martinsram3k/Node-Smart-Clock/pcb/esp_smart_clock/esp_smart_clock.kicad_sch

## KiCad design pcb/esp_smart_clock/esp_smart_clock.kicad_sch (2026-01-16)

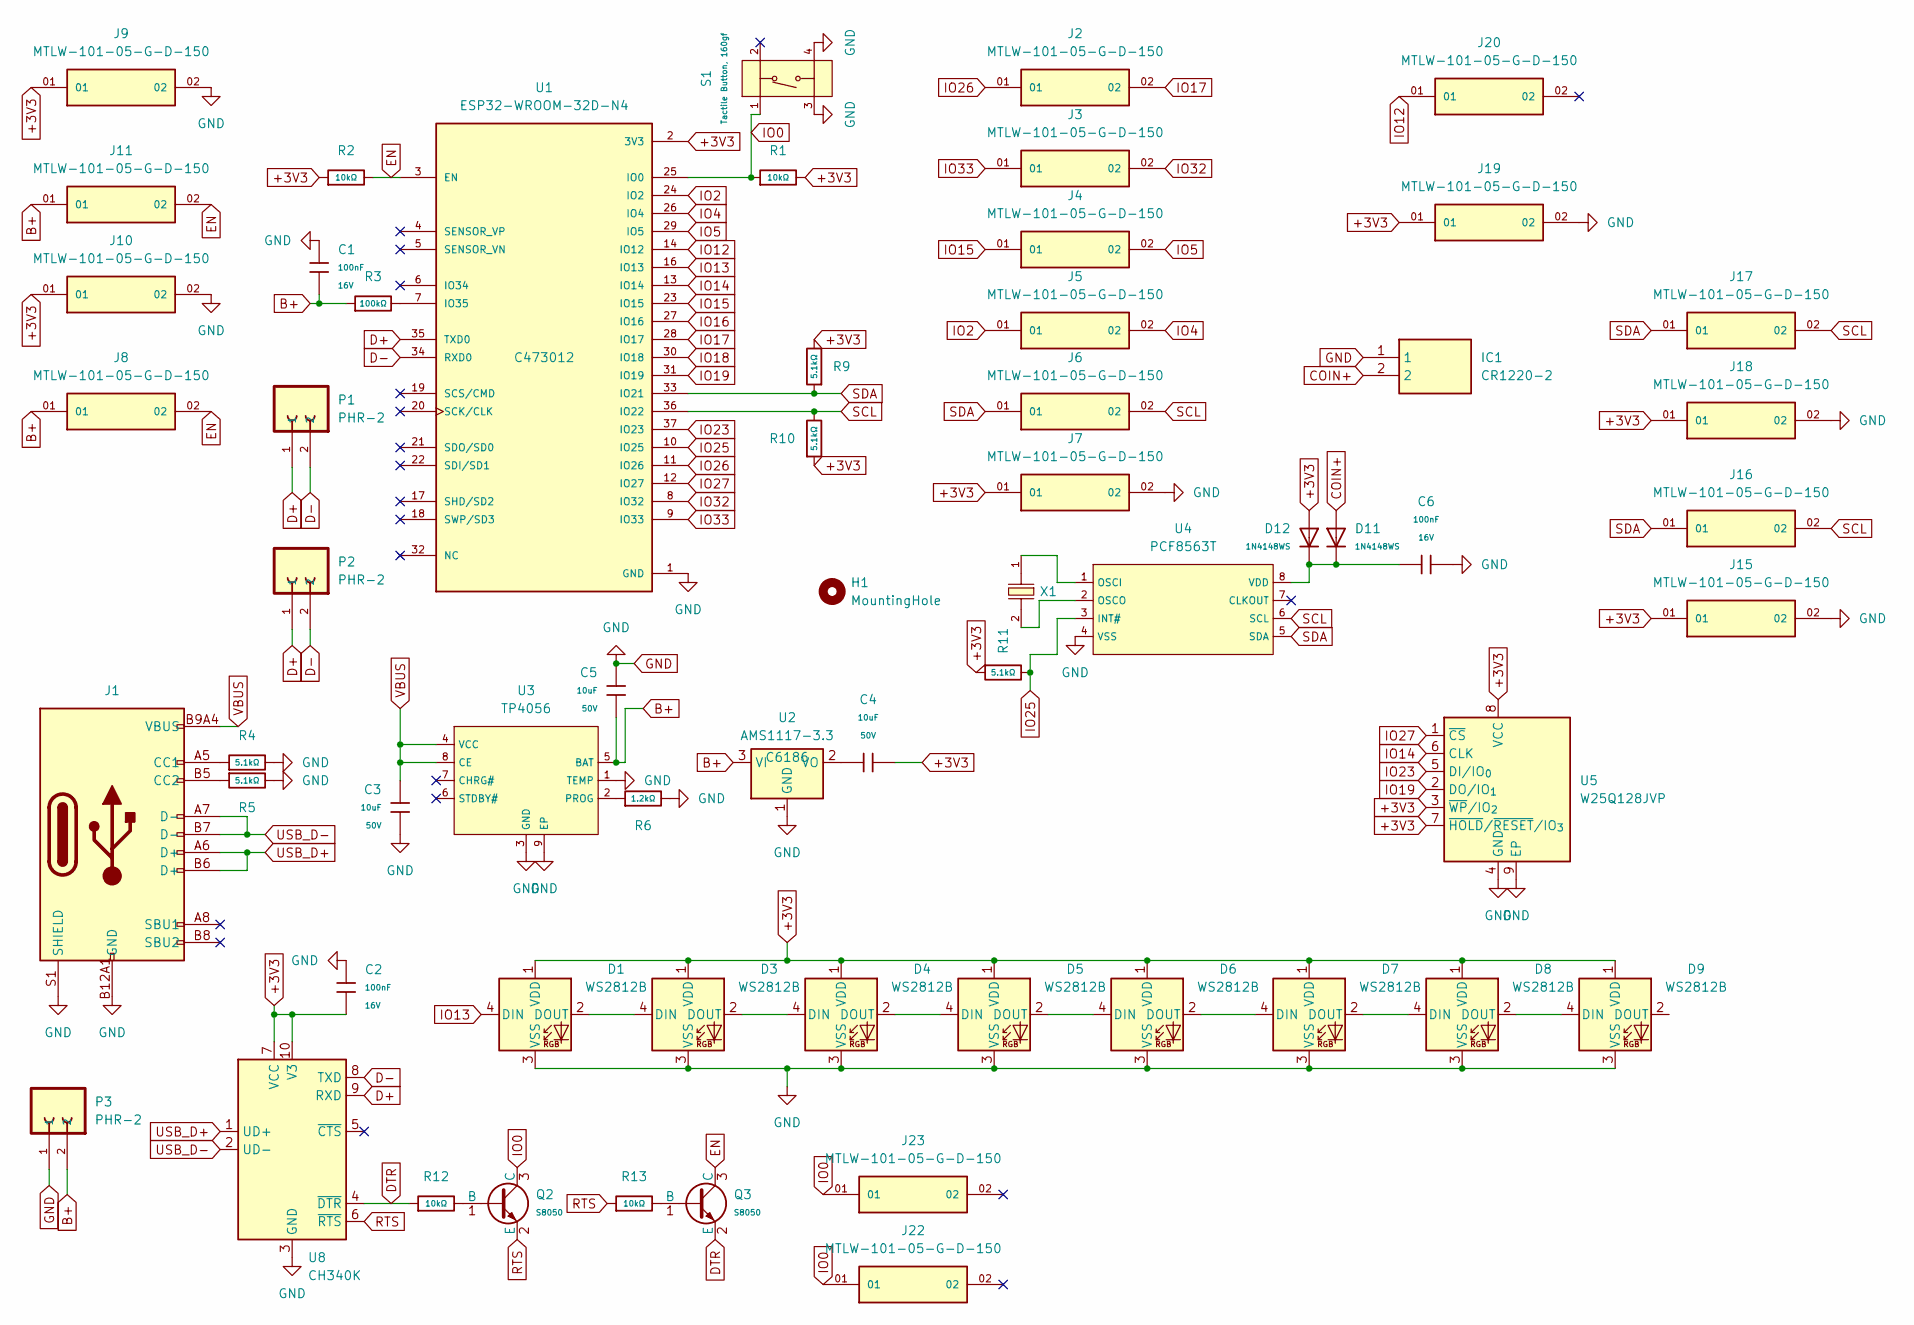
[picture p9: schematic esp_smart_clock.kicad_sch]

Parts:
C1, C2, C6: 100nF; C_0402; Voltage Rated 16V; Tolerance ±10%; Part CL05B104KO5NNNC; LCSC C1525
C3, C4, C5: 10uF; C_1206; Voltage Rated 50V; Tolerance ±10%; Part CL31A106KBHNNNE; LCSC C13585
D1, D3, D4, D5, D6, D7, D8, D9: WS2812B; LED_WS2812B_PLCC4_5.0x5.0mm_P3.2mm; LCSC C22461793
D11, D12: 1N4148WS; D_SOD-323; Forward Voltage (Vf@If) 1.25V@150mA; Reverse Voltage (Vr) 100V; Part 1N4148WS; LCSC C2128
H1: MountingHole; MountingHole_2.1mm
IC1: CR1220-2; BAT-SMD_CR1220-2; Manufacturer_Part_Number CR1220-2; LCSC C70381
J1: Connector, USB-TYPE-C-16P; TYPE-C-SMD_HX-TYPE-C-16PIN; LCSC C2927039
J2, J3, J4, J5, J6, J7, J8, J9, J10, J11, J15, J16, J17, J18, J19, J20, J22, J23: MTLW-101-05-G-D-150; SAMTEC_MTLW-101-05-G-D-150; PARTREV R
P1, P2, P3: PHR-2; JST_PHR-2; LCSC C2319
Q2, Q3: S8050; Q_SOT-23; Part S8050; LCSC C364312
R1, R2, R12, R13: 10kΩ; R_0402; Overload Voltage (Max) 50V; Tolerance ±1%; Part 0402WGF1002TCE; LCSC C25744
R3: 100kΩ; R_0402; Overload Voltage (Max) 50V; Tolerance ±1%; Part 0402WGF1003TCE; LCSC C25741
R4, R5, R9, R10, R11: 5.1kΩ; R_0402; Overload Voltage (Max) 50V; Tolerance ±1%; Part 0402WGF5101TCE; LCSC C25905
R6: 1.2kΩ; R_0402; Overload Voltage (Max) 50V; Tolerance ±1%; Part 0402WGF1201TCE; LCSC C25862
S1: Tactile Button, 160gf; SW-SMD_4P-L5.1-W5.1-P3.70-LS6.5-TL-2; Voltage Rating (Dc) 12V; Part TS-1187A-B-A-B; LCSC C318884
U1: ESP32-WROOM-32D-N4; MODULE_ESP32-WROOM-32D-N4; PARTREV 1.9; LCSC C473012
U2: AMS1117-3.3; SOT-223-3_TabPin2; LCSC C6186
U3: TP4056; ESOP-8_L4.9-W3.9-P1.27-LS6.0-BL-EP; Part TP4056-42-ESOP8; LCSC C16581
U4: PCF8563T; SOIC-8_L5.0-W4.0-P1.27-LS6.0-BL; Operating Voltage 1V~5.5V; Part PCF8563T/5,518; LCSC C7440
U5: W25Q128JVP; WSON-8-1EP_6x5mm_P1.27mm_EP3.4x4.3mm
U8: CH340K; SSOP-10-1EP_3.9x4.9mm_P1mm_EP2.1x3.3mm; LCSC C968586
X1: Q13FC1350000400; FC-135R_L3.2-W1.5; Frequency Tolerance ±20ppm; Part Q13FC13500004; LCSC C32346

Connections:
+3V3: C2.2, C4.2, D1.1 (VDD), D3.1 (VDD), D4.1 (VDD), D5.1 (VDD), D6.1 (VDD), D7.1 (VDD), D8.1 (VDD), D9.1 (VDD), D12.2, J7.01, J9.01, J10.01, J15.01, J18.01, J19.01, R1.2, R2.1, R9.2, R10.1, R11.1, U1.2 (3V3), U5.3 (~WP/IO_{2}), U5.7 (~HOLD/~RESET/IO_{3}), U5.8 (VCC), U8.7 (VCC), U8.10 (V3)
B+: C1.2, C5.2, J8.01, J11.01, P3.2, R3.1, U2.3 (VI), U3.5 (BAT)
COIN+: D11.2, IC1.2
D+: P1.1, P2.1, U1.35 (TXD0), U8.9 (RXD)
D-: P1.2, P2.2, U1.34 (RXD0), U8.8 (TXD)
DTR: Q3.2 (E), R12.1, U8.4 (~DTR)
EN: J8.02, J11.02, Q3.3 (C), R2.2, U1.3 (EN)
GND: C1.1, C2.1, C3.2, C5.1, C6.2, D1.3 (VSS), D3.3 (VSS), D4.3 (VSS), D5.3 (VSS), D6.3 (VSS), D7.3 (VSS), D8.3 (VSS), D9.3 (VSS), IC1.1, J1.A12B1 (GND), J1.B12A1 (GND), J1.S1 (SHIELD), J7.02, J9.02, J10.02, J15.02, J18.02, J19.02, P3.1, R4.2, R5.2, R6.2, S1.3 (C), S1.4 (D), U1.1 (GND), U1.15 (GND), U1.38 (GND), U1.39_1 (GND), U1.39_2 (GND), U1.39_3 (GND), U1.39_4 (GND), U1.39_5 (GND), U1.39_6 (GND), U1.39_7 (GND), U1.39_8 (GND), U1.39_9 (GND), U1.39_10 (GND), U1.39_11 (GND), U1.39_12 (GND), U1.39_13 (GND), U1.39_14 (GND), U1.39_15 (GND), U1.39_16 (GND), U1.39_17 (GND), U1.39_18 (GND), U1.39_19 (GND), U1.39_20 (GND), U1.39_21 (GND), U2.1 (GND), U3.1 (TEMP), U3.3 (GND), U3.9 (EP), U4.4 (VSS), U5.4 (GND), U5.9 (EP), U8.3 (GND), U8.11 (GND)
IO0: J22.01, J23.01, Q2.3 (C), R1.1, S1.1 (A), U1.25 (IO0)
IO2: J5.01, U1.24 (IO2)
IO4: J5.02, U1.26 (IO4)
IO5: J4.02, U1.29 (IO5)
IO12: J20.01, U1.14 (IO12)
IO13: D1.4 (DIN), U1.16 (IO13)
IO14: U1.13 (IO14), U5.6 (CLK)
IO15: J4.01, U1.23 (IO15)
IO16: U1.27 (IO16)
IO17: J2.02, U1.28 (IO17)
IO18: U1.30 (IO18)
IO19: U1.31 (IO19), U5.2 (DO/IO_{1})
IO23: U1.37 (IO23), U5.5 (DI/IO_{0})
IO25: R11.2, U1.10 (IO25), U4.3 (INT#)
IO26: J2.01, U1.11 (IO26)
IO27: U1.12 (IO27), U5.1 (~CS)
IO32: J3.02, U1.8 (IO32)
IO33: J3.01, U1.9 (IO33)
unnamed: C4.1, U2.2 (VO)
unnamed: C6.1, D11.1, D12.1, U4.8 (VDD)
unnamed: D1.2 (DOUT), D3.4 (DIN)
unnamed: D3.2 (DOUT), D4.4 (DIN)
unnamed: D4.2 (DOUT), D5.4 (DIN)
unnamed: D5.2 (DOUT), D6.4 (DIN)
unnamed: D6.2 (DOUT), D7.4 (DIN)
unnamed: D7.2 (DOUT), D8.4 (DIN)
unnamed: D8.2 (DOUT), D9.4 (DIN)
unnamed: J1.A5 (CC1), R4.1
unnamed: J1.B5 (CC2), R5.1
unnamed: Q2.1 (B), R12.2
unnamed: Q3.1 (B), R13.2
unnamed: R3.2, U1.7 (IO35)
unnamed: R6.1, U3.2 (PROG)
unnamed: U4.1 (OSCI), X1.1
unnamed: U4.2 (OSCO), X1.2
RTS: Q2.2 (E), R13.1, U8.6 (~RTS)
SCL: J6.02, J16.02, J17.02, R10.2, U1.36 (IO22), U4.6 (SCL)
SDA: J6.01, J16.01, J17.01, R9.1, U1.33 (IO21), U4.5 (SDA)
USB_D+: J1.A6 (D+), J1.B6 (D+), U8.1 (UD+)
USB_D-: J1.A7 (D-), J1.B7 (D-), U8.2 (UD-)
VBUS: C3.1, J1.A9B4 (VBUS), J1.B9A4 (VBUS), U3.4 (VCC), U3.8 (CE)
